aetel/3D-printer/prusa_i3/Printed Parts/z-axis-bottom.stl

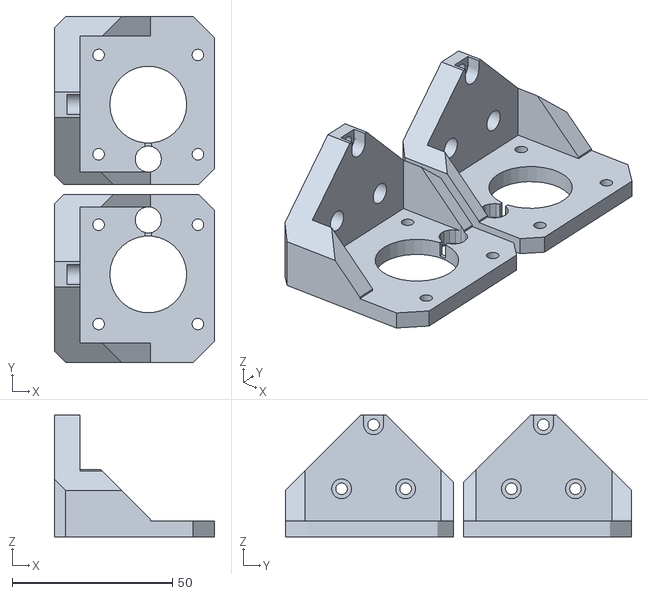
[picture p16: CAD file, 2017-11-05]
prusa_i3/Printed Parts/z-axis-bottom.stl
50.0 x 108.0 x 38.0
