aetel/3D-printer/prusa_i3/Printed Parts/extruder/body_and _cover/extruder-coverMK8S18.stl

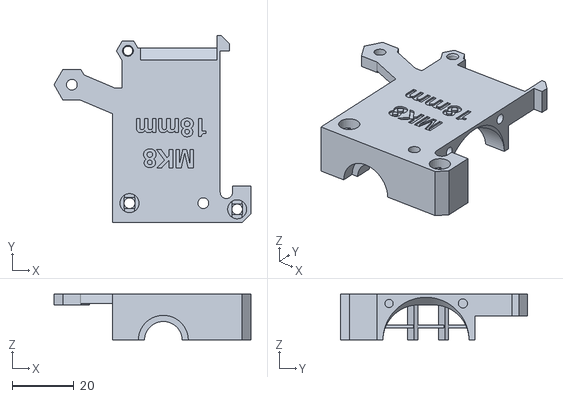
[picture p17: CAD file, 2018-03-08]
prusa_i3/Printed Parts/extruder/body_and _cover/extruder-coverMK8S18.stl
64.0 x 60.8 x 14.8
