aetel/3D-printer/prusa_i3/Printed Parts/LCD/LCD-holder-B.STL

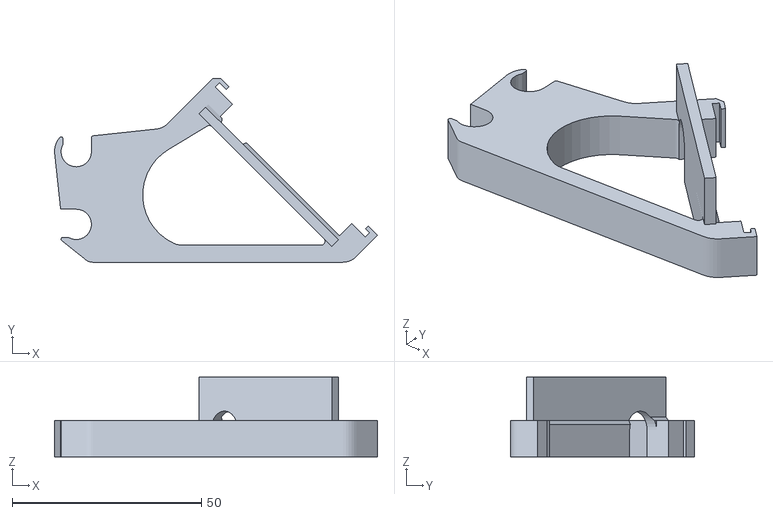
[picture p18: CAD file, 2017-11-05]
prusa_i3/Printed Parts/LCD/LCD-holder-B.STL
85.2 x 48.4 x 21.1
