aetel/3D-printer/prusa_i3/Printed Parts/spool-holder/spool-holder-spindle-part2.stl

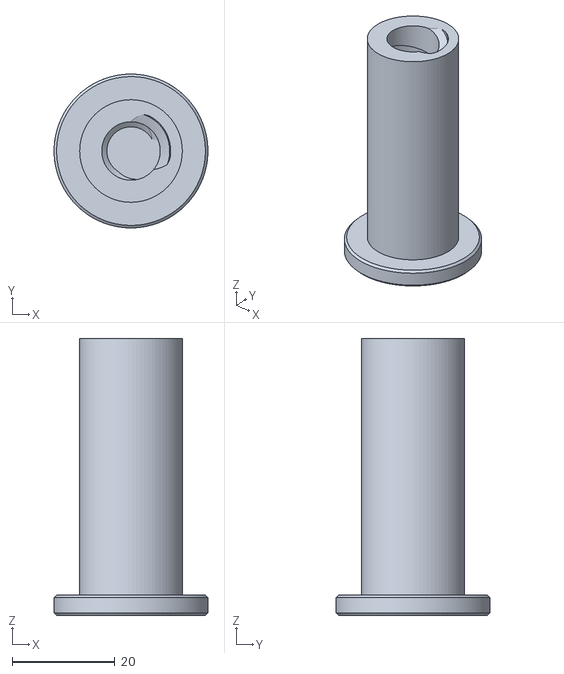
[picture p19: CAD file, 2020-10-20]
prusa_i3/Printed Parts/spool-holder/spool-holder-spindle-part2.stl
30.0 x 30.0 x 54.0
