aetel/3D-printer/prusa_i3/Printed Parts/y-distance.stl

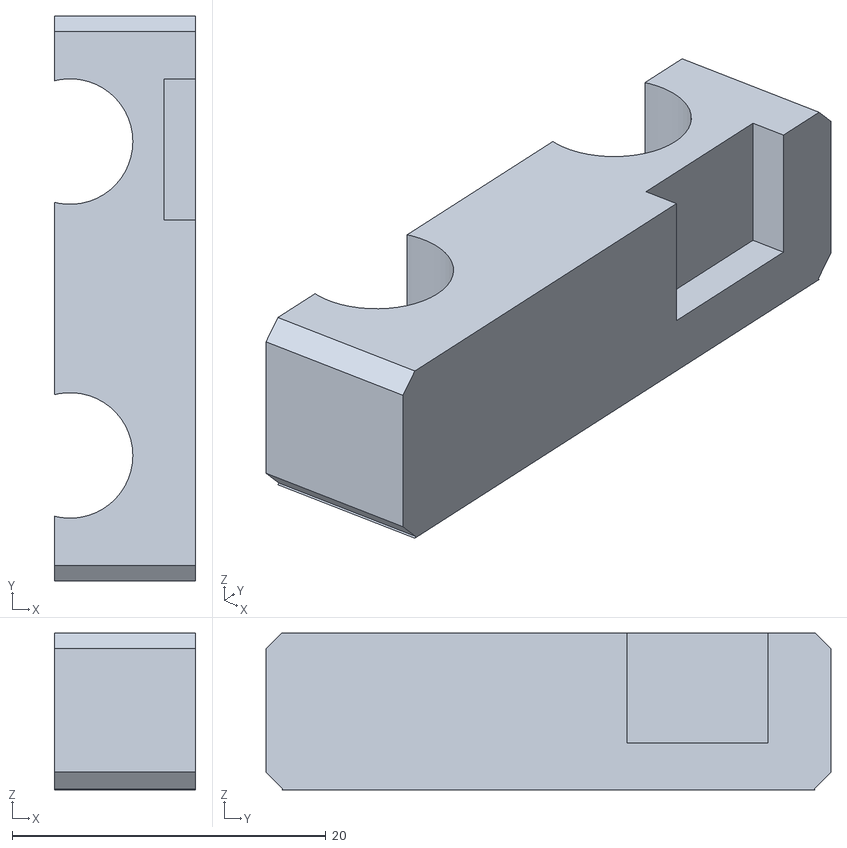
[picture p20: CAD file, 2017-11-05]
prusa_i3/Printed Parts/y-distance.stl
9.00 x 36.0 x 10.0
