aetel/3D-printer/prusa_i3/Printed Parts/PSU-y-part.stl

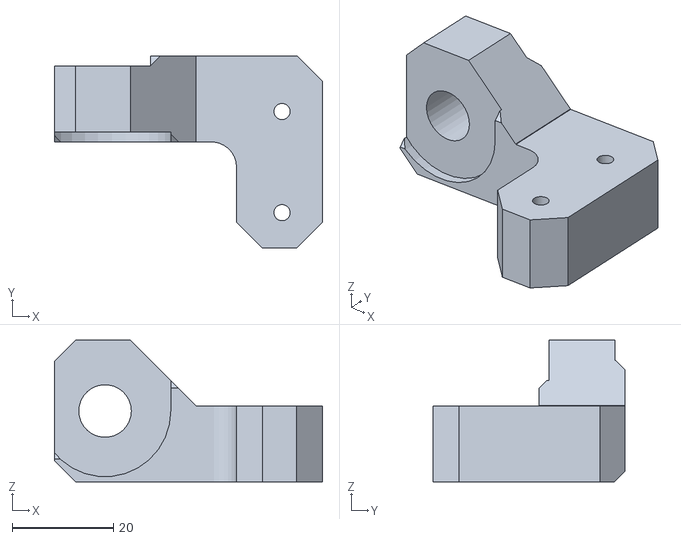
[picture p21: CAD file, 2017-11-05]
prusa_i3/Printed Parts/PSU-y-part.stl
53.0 x 38.0 x 28.0
