aetel/3D-printer/prusa_i3/Printed Parts/extruder/body_and _cover/extruder-bodyMK8S8.stl

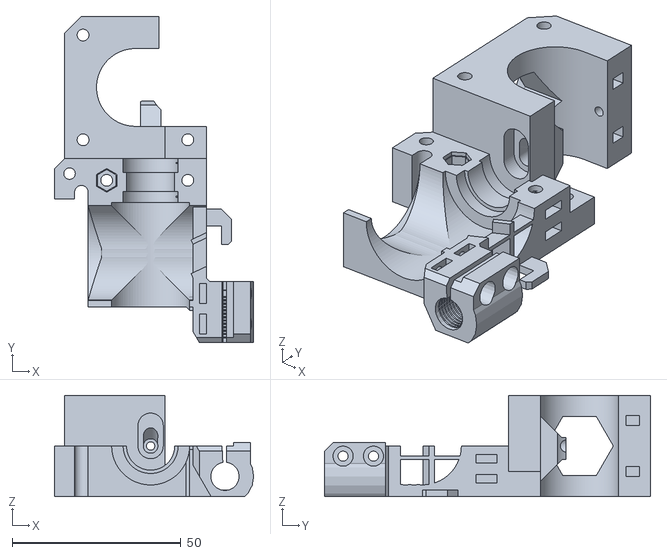
[picture p22: CAD file, 2017-11-05]
prusa_i3/Printed Parts/extruder/body_and _cover/extruder-bodyMK8S8.stl
59.0 x 96.5 x 30.0
