aetel/3D-printer/prusa_i3/Printed Parts/y-belt-holder.stl

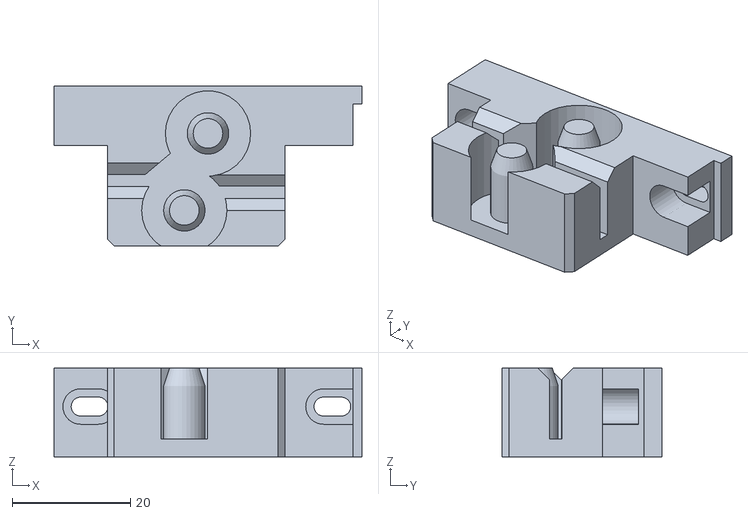
[picture p23: CAD file, 2017-11-05]
prusa_i3/Printed Parts/y-belt-holder.stl
52.0 x 27.0 x 15.0
