aetel/3D-printer/prusa_i3/Printed Parts/x-carriage.stl

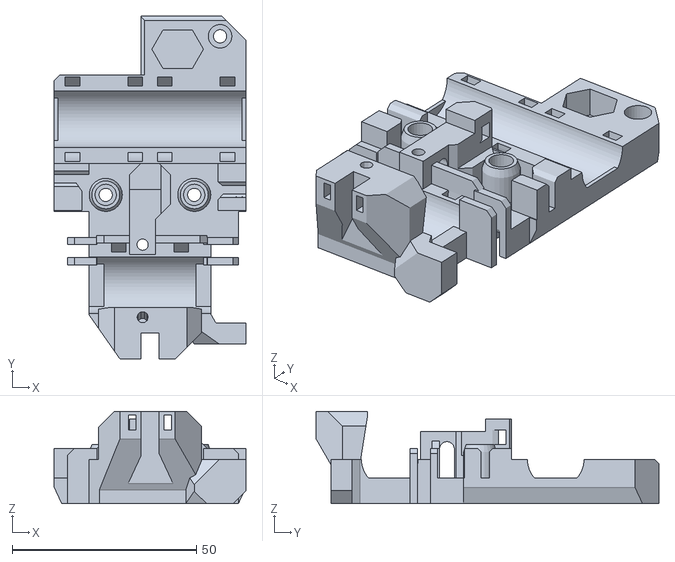
[picture p24: CAD file, 2017-11-05]
prusa_i3/Printed Parts/x-carriage.stl
52.0 x 93.0 x 25.0
