aetel/3D-printer/prusa_i3/Printed Parts/z-axis-top.stl

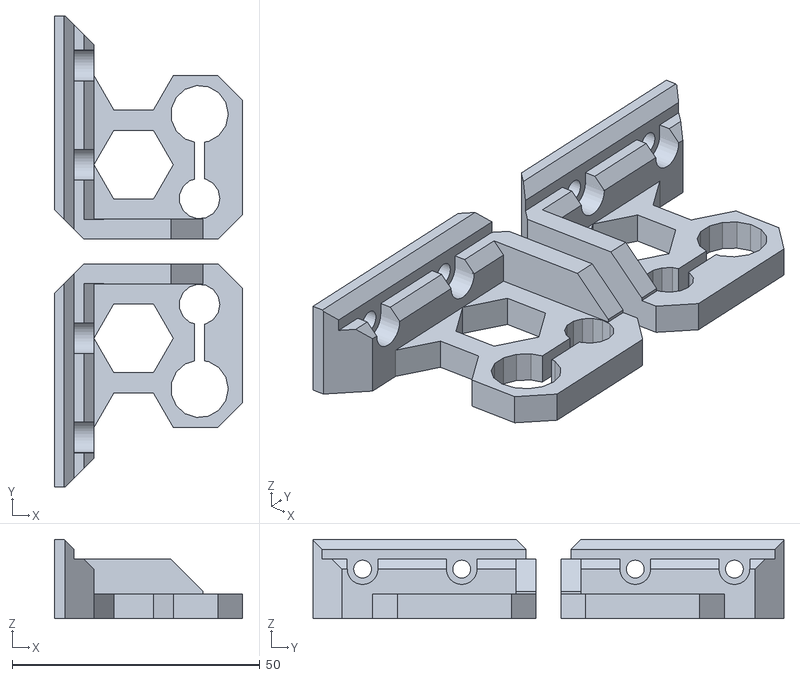
[picture p25: CAD file, 2017-11-05]
prusa_i3/Printed Parts/z-axis-top.stl
38.0 x 95.0 x 16.0
