aetel/3D-printer/prusa_i3/Printed Parts/y-corners.stl

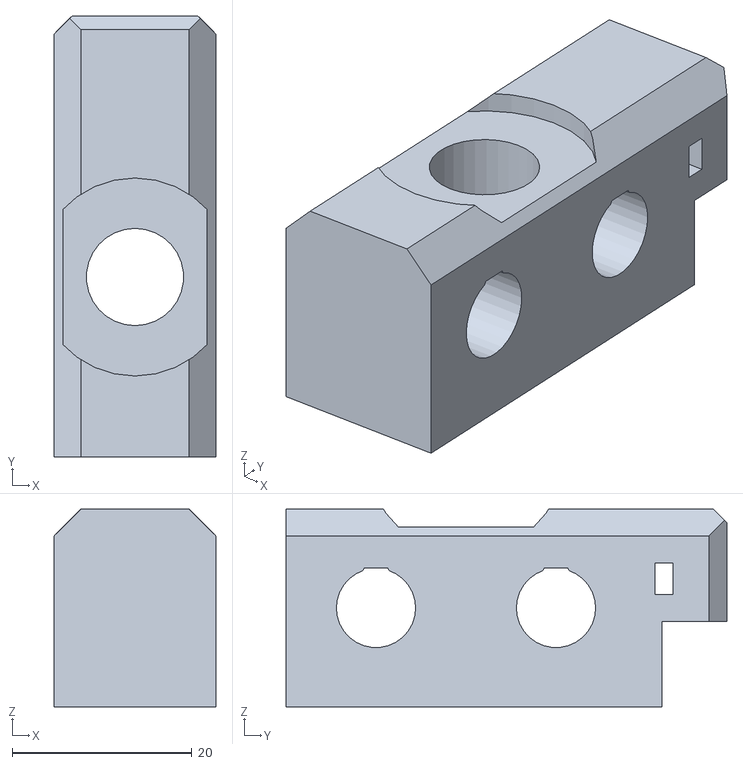
[picture p26: CAD file, 2017-11-05]
prusa_i3/Printed Parts/y-corners.stl
18.0 x 49.0 x 22.0
