aetel/3D-printer/prusa_i3/Printed Parts/y-idler.stl

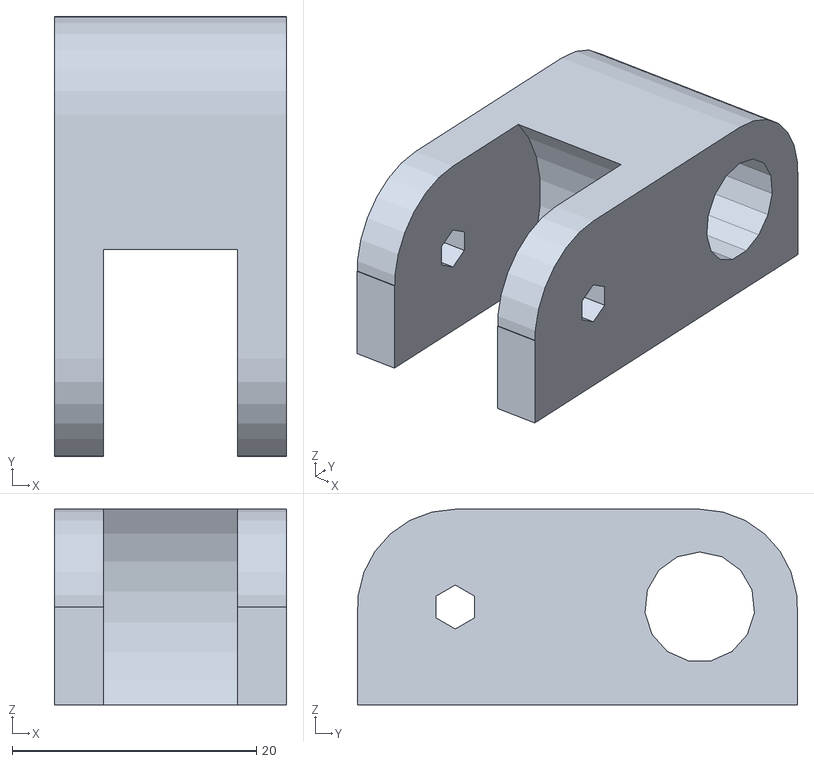
[picture p27: CAD file, 2017-11-05]
prusa_i3/Printed Parts/y-idler.stl
19.0 x 36.0 x 16.0
