aetel/3D-printer/prusa_i3/Printed Parts/aetel-box.stl

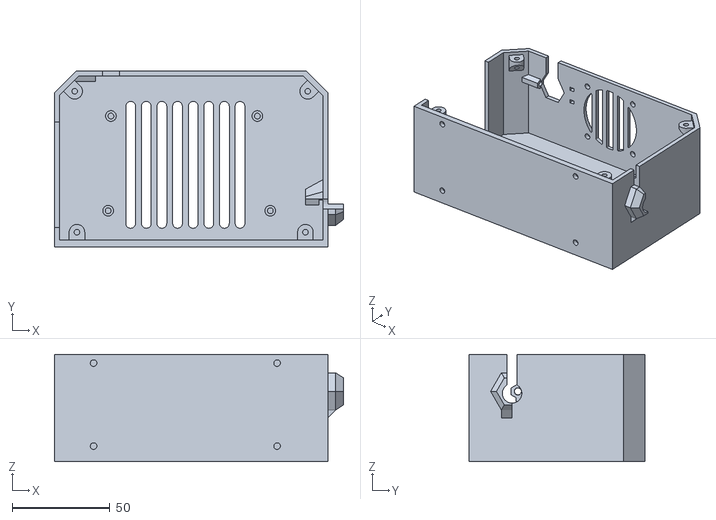
[picture p28: CAD file, 2017-11-05]
prusa_i3/Printed Parts/aetel-box.stl
148.0 x 90.0 x 55.0
