aetel/3D-printer/prusa_i3/Printed Parts/y-motor.stl

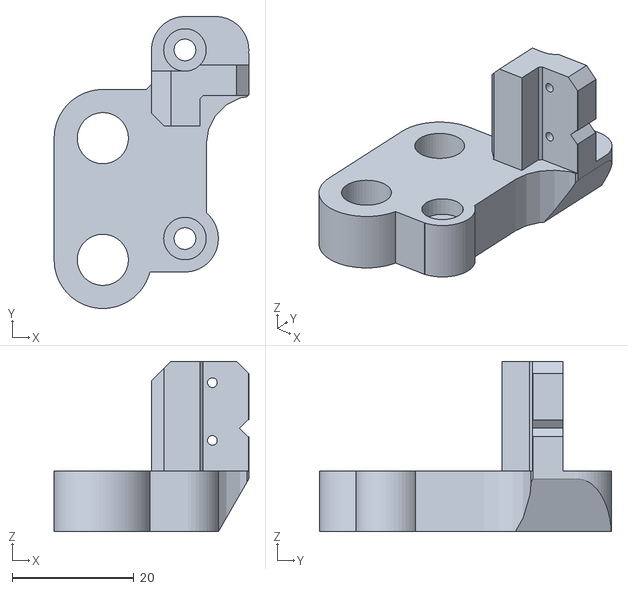
[picture p29: CAD file, 2017-11-05]
prusa_i3/Printed Parts/y-motor.stl
32.0 x 48.0 x 28.0
